Keaton-Ruthardt/Masters_Thesis/references/smart_baseball_references.md

# Smart Baseball / Instrumented Ball References

Compiled for MastersBall thesis project. Organized by topic.

---

## McGinnis IMU Baseball (University of Michigan)

- McGinnis, R.S.; Perkins, N.C. "A Highly Miniaturized, Wireless Inertial Measurement Unit for Characterizing the Dynamics of Pitched Baseballs and Softballs." *Sensors* 2012, 12(9), 11933–11945. https://www.mdpi.com/1424-8220/12/9/11933
- PMC Full Text: https://pmc.ncbi.nlm.nih.gov/articles/PMC3478818/
- McGinnis, R.S.; Perkins, N.C. "Pitcher Training Aided by Instrumented Baseball." *Procedia Engineering* 2012, 34, 580–585. (9th ISEA Conference). https://www.sciencedirect.com/science/article/pii/S1877705812017122
- McGinnis, R.S. "Advancing Applications of IMUs in Sports Training and Biomechanics." PhD Dissertation, University of Michigan, 2013. https://deepblue.lib.umich.edu/handle/2027.42/97947
- McGinnis, R.S.; Perkins, N.C.; King, K. "Miniaturized Wireless IMU Enables Low-Cost Baseball Pitching Training Aid." 35th Annual Meeting of the American Society of Biomechanics, Long Beach, CA, 2011. https://www.researchgate.net/publication/266458149_Miniaturized_Wireless_IMU_Enables_Low-Cost_Baseball_Pitching_Training_Aid
- King, K.; Yoon, S.W.; Perkins, N.C.; Najafi, K. "Wireless MEMS Inertial Sensor System for Golf Swing Dynamics." *Sensors and Actuators A: Physical* 2008, 141(2). https://www.sciencedirect.com/science/article/abs/pii/S092442470700667X
- King, K.; Perkins, N.C.; Churchill, H.; McGinnis, R.; Doss, R. "Bowling Ball Dynamics Revealed by Miniature Wireless MEMS Inertial Measurement Unit." *Sports Engineering* 2011, 13, 95–104. https://link.springer.com/article/10.1007/s12283-010-0054-z
- King, K.; Hough, J.; McGinnis, R.; Perkins, N.C. "A New Technology for Resolving the Dynamics of a Swinging Bat." *Sports Engineering* 2012, 15, 41–52.
- Perkins Lab Website (Athletic Performance): https://kmperk.wixsite.com/perkins/athletic-performance
- Perkins Faculty Page, U-M Mechanical Engineering: https://me.engin.umich.edu/people/faculty/noel-perkins/
- McGinnis Google Scholar: https://scholar.google.com/citations?user=IA5-EMcAAAAJ&hl=en

---

## Diamond Kinetics

### Patents
- US 7,021,140 — "Electronic measurement of the motion of a moving body of sports equipment." Perkins, N.C. Assignee: Regents of the University of Michigan. 2006. https://patents.google.com/patent/US7021140B2/en
- US 7,234,351 B2 — "Electronic measurement of the motion of a moving body of sports equipment." Perkins, N.C. Assignee: Regents of the University of Michigan. 2007. https://patents.google.com/patent/US7234351B2/en
- US 8,944,939 B2 — "Inertial Measurement of Sports Motion." Clark, W.W.; Romeiko, J.R. Assignee: University of Pittsburgh. 2015. https://patents.google.com/patent/US8944939B2/en
- US 9,032,794 B2 — "Pitcher training apparatus and method using a ball with an embedded inertial measurement unit." Perkins, N.; McGinnis, R. Assignee: Regents of the University of Michigan. 2015. https://patents.google.com/patent/US9032794B2/en
- US 10,888,735 B2 — "Calibration of initial orientation and position of sports equipment and body segments for inertial sensors." Clark, W.W.; Zhang, M.; Ressler, M. Assignee: Diamond Kinetics, Inc. 2021. https://patents.google.com/patent/US10888735B2/en
- US 11,083,951 — "Ball spin rate measurement system and method." Zhang, M.; Rittenhouse, J.M.; Ressler, M.J.; Clark, W.W. Assignee: Diamond Kinetics, Inc. 2021. https://patents.justia.com/patent/11083951
- Diamond Kinetics Patent Information Page: https://www.diamondkinetics.com/patent-information/patent

### Press & Technical Coverage
- U-M Innovation Partnerships: "U-M startup Diamond Kinetics releases PitchTracker for baseball pitching data." https://innovationpartnerships.umich.edu/stories/u-m-startup-diamond-kinetics-releases-pitchtracker-for-baseball-pitching-data/
- U-M ME: "Professor Noel Perkins' micro-sensor a game changer." https://me.engin.umich.edu/news-events/news/professor-noel-perkins-micro-sensor-game-changer/
- PittWire: "MLB, USA Softball and kids alike use a Pitt inventor's smart bats and balls." https://www.pittwire.pitt.edu/pittwire/features-articles/mlb-usa-softball-pitt-startup-diamond-kinetics
- Pitt Innovation: Diamond Kinetics Startup Profile. https://www.innovation.pitt.edu/pitt-startups/diamond-kinetics/
- Pitt Innovation Blog: "Take a Swing at Improving Human Performance." https://blog.innovation.pitt.edu/take-a-swing-at-improving-human-performance
- Technical.ly: "Diamond Kinetics founder on 10 years of rapid growth." https://technical.ly/startups/diamond-kinetics-mlb-founder-growth/
- Crain's Detroit: "With UM patent, it's better batter up." https://www.crainsdetroit.com/article/20130421/NEWS/304219991/with-um-patent-its-better-batter-up
- NextPittsburgh: "A high-tech baseball that tracks performance." https://nextpittsburgh.com/latest-news/diamond-kinetics-introduces-high-tech-baseball-pro-amateur-pitchers-track-performance/
- GeekWire: "Diamond Kinetics uses embedded sensors to help MLB batters and pitchers." https://www.geekwire.com/2018/diamond-kinetics-uses-embedded-sensors-help-mlb-batters-pitchers-improve-performance/
- Patent Forecast: "Diamond Kinetics Strikes A Deal With the MLB." https://www.patentforecast.com/2022/04/07/diamond-kinetics-strikes-a-deal-with-the-mlb/
- Driveline Baseball: "PitchTracker, Rapsodo, and Pitch Tracking Technologies." https://www.drivelinebaseball.com/2018/07/diamond-kinetics-pitchtracker-rapsodo-pitch-tracking-technologies/
- Diamond Kinetics Technology Page: https://www.diamondkinetics.com/technology
- FCC Report (FCC ID 2ABWR-DKT003): https://fcc.report/FCC-ID/2ABWR-DKT003

---

## PitchLogic (F5 Sports)

### Technical Sources
- Nordic Semiconductor Case Study: "F5 Sports baseball uses built-in sensors to give players and coaches live body movement and pitch performance metrics." https://www.nordicsemi.com/Nordic-news/2019/03/F5-Sports-baseball-uses-built-in-sensors-to-give-players-and-coaches-live-body-movement
- PitchLogic — How It Works: https://pitchlogic.com/howitworks
- PitchLogic — Metrics: https://pitchlogic.com/metrics
- PitchLogic Pro: https://pitchlogic.com/pitchlogic-pro
- F5 Sports Durability Test (One Year): https://pitchlogic.com/blogs/a-durability-test-on-the-pitchlogic-baseball-one-year-later

### Validation & Reviews
- Samford University Center for Sports Analytics: "Validating pitchLogic: Assessing the New Smart Baseball." 2020. https://www.samford.edu/sports-analytics/fans/2020/Validating-pitchLogic-Assessing-the-New-Smart-Baseball
- Driveline Baseball: "PitchLogic" (practical usage guide). 2022. https://www.drivelinebaseball.com/2022/07/pitchlogic/
- Baseball Aerodynamics Blog: "Training Kids with Smart Baseballs" (Post 71). 2021. https://baseballaero.com/2021/11/13/training-kids-with-smart-baseballs-post-71/
- TopVelocity: "Pitch Tracking Technologies: Trackman, Rapsodo & More." 2024. https://www.topvelocity.net/2024/05/16/pitch-tracking-technologies-trackman-rapsodo-more/
- The Robby Row Show: PitchLogic Review. https://therobbyrowshow.com/pitch-logic/

### Company & Press
- WRAL TechWire: "W-S sports tech company F5 Sports continues to fundraise, now with newly patented pitchLogic system." 2022. https://wraltechwire.com/2022/06/24/w-s-sports-tech-company-f5-sports-continues-to-fundraise-now-with-newly-patented-pitchlogic-system/
- Wake Forest Baseball Partnership: https://godeacs.com/news/2023/9/18/wake-forest-university-baseball-to-utilize-f5-sports-pitchlogic-smart-baseball
- ABCA Partnership: https://www.abca.org/ABCA/ABCA/News/2023/ABCA_and_pitchLogic_Announce_New_Partnership.aspx
- Apple App Store: https://apps.apple.com/us/app/pitchlogic/id1448402158

---

## 2024 MDPI Force Sensor Baseball

- "Sensor-Embedded Baseball for Measurement of Finger Force Characteristics." *Sensors* 2024, 24(11), 3523. https://www.mdpi.com/1424-8220/24/11/3523
- PMC: https://pmc.ncbi.nlm.nih.gov/articles/PMC11175286/

---

## Smart Cricket Balls

- Fuss, F.K.; Lythgo, N.; Smith, R.M.; Benson, A.C.; Gordon, B. "Development of a Smart Cricket Ball for Advanced Performance Analysis of Bowling." *Procedia Technology* 2015, 20, 133–137. https://www.researchgate.net/publication/283271775_Development_of_a_Smart_Cricket_Ball_for_Advanced_Performance_Analysis_of_Bowling
- Fuss, F.K. et al. "Mobile Computing with a Smart Cricket Ball: Discovery of Novel Performance Parameters and Their Practical Application to Performance Analysis, Advanced Profiling, Tactical Insights, and Talent Identification of Spin Bowlers." *Sensors* 2021, 21(20), 6942. https://www.mdpi.com/1424-8220/21/20/6942
- Nordic Semiconductor: "Sportcor SmartBall employs nRF52840 to send tracking data from Kookaburra Sports SmartBall to app." https://www.nordicsemi.com/Nordic-news/2019/10/Sportcor-Smartball-employs-nRF52840-to-send-tracking-data-from-Kookaburra-Sports-Smartball-to-app
- Electronics Weekly: "Smart Cricket Ball Measures Bowling Performance." https://www.electronicsweekly.com/blogs/gadget-master/sensors/smart-cricket-ball-measures-bowling-performance-2020-01/

---

## Smart Golf Balls & Other Smart Sports Balls

- GENIUS Golf Ball (OnCore): https://geniusball.golf/
- OnCore Golf Technology / Patents: https://www.oncoregolf.com/technology/
- First Call Golf: "The First Smart Golf Ball That Captures Crucial Putting Data — GENIUS." 2026. https://www.firstcallgolf.com/industry-news/release/2026-01-15/the-first-smart-golf-ball-that-captures-crucial-putting-data-genius-to-make-groundbreaking-debut-at-pg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
- Smart Golf Ball with Embedded Microsystem (University Project, MCEN 4228): http://mirandabutler.github.io/img/mechanical/MSreport.pdf
- Fraunhofer: Microsystem Technologies for Smart Golf Balls ("eGrains"). https://publica.fraunhofer.de/entities/publication/e8bcb660-518a-4688-a181-c66124ebc0aa
- SoccerBible: "Closer Look — Adidas miCoach Smart Ball." https://www.soccerbible.com/performance/football-equipment/closer-look-adidas-micoach-smartball/

---

## Baseball Physics & Biomechanics

- Penn State — Forces Between Bat and Ball (Dr. Dan Russell): https://www.acs.psu.edu/drussell/bats/impulse.html
- University of Illinois — Dynamics of the Baseball-Bat Collision (Prof. Alan Nathan): https://baseball.physics.illinois.edu/AJP-Nov2000.pdf
- University of Illinois — Baseball Aerodynamics: https://baseball.physics.illinois.edu/aero.html
- NASA — Forces on a Baseball (Beginner's Guide to Aeronautics): https://www1.grc.nasa.gov/beginners-guide-to-aeronautics/forces-on-a-baseball/
- ACS — "What's in Baseballs: Materials Explain the Spike in Home Runs." *Chemical & Engineering News* 2017, 95(26). https://cen.acs.org/articles/95/i26/s-baseballs-materials-explain-spike.html
- Baseball Rules Academy — Official Rule 3.01 (The Ball): https://baseballrulesacademy.com/official-rule/mlb/3-01-the-ball/
- University of Illinois — Inertial Sensors in Baseball: https://baseball.physics.illinois.edu/batsensors.html
- MIT Media Lab — "IMU Arrays: The Biomechanics of Baseball Pitching." Paradiso, J. et al. 2006. https://www.media.mit.edu/publications/imu-arrays-the-biomechanics-of-baseball-pitching/
- MIT Media Lab PDF: https://resenv.media.mit.edu/pubs/papers/2006-06-IMU-Baseball.pdf

---

## High-g Sensor Technology & Shock Survival

- Analog Devices — "Surviving the Extremes" (MEMS in High-Shock Environments): https://www.analog.com/en/resources/analog-dialogue/articles/surviving-the-extremes.html
- ADXL375 High-g Accelerometer (200g, digital): https://www.adafruit.com/product/5374
- Blast Motion Bat Sensor (10,000g survival housing): https://blastmotion.com/products/baseball/
- Garmin Impact Bat Sensor: https://www.garmin.com/en-US/p/579018/

---

## Sensor Datasheets (Components in MastersBall Project)

- King et al. — Instrumented Cricket Ball Spin Measurement (19×24mm PCB, 3g): https://www.sciencedirect.com/science/article/pii/S1877705812016360

---

*Last updated: March 2026*
*Compiled for MastersBall instrumented baseball thesis project*
