Keaton-Ruthardt/Masters_Thesis/hardware/smartball_PCB.pdf

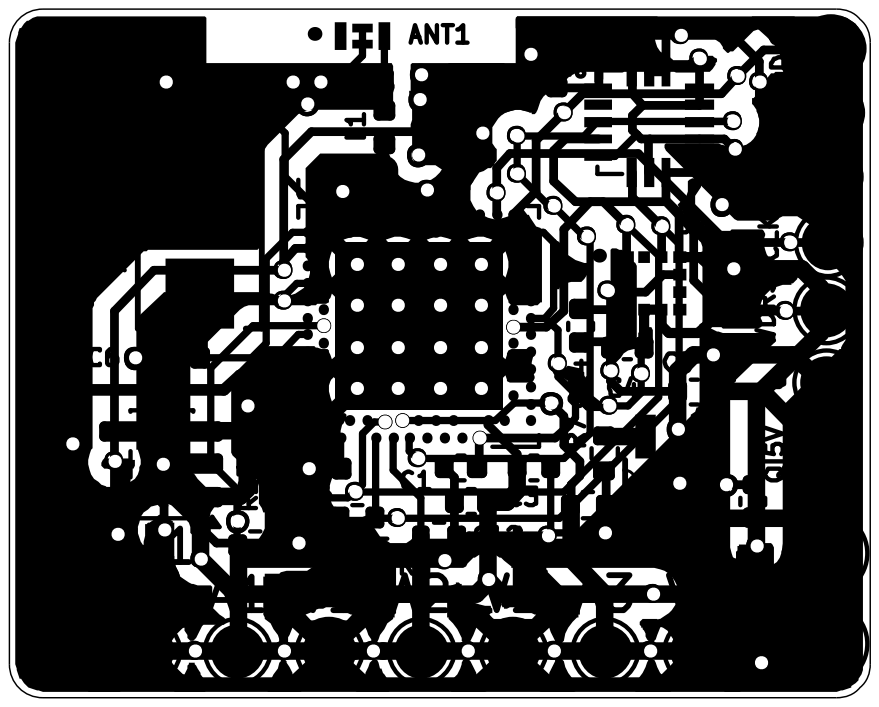
[picture p14: page 1]
