Keaton-Ruthardt/Masters_Thesis/figures/wiring+xaio+usb-c-adapater.jpeg

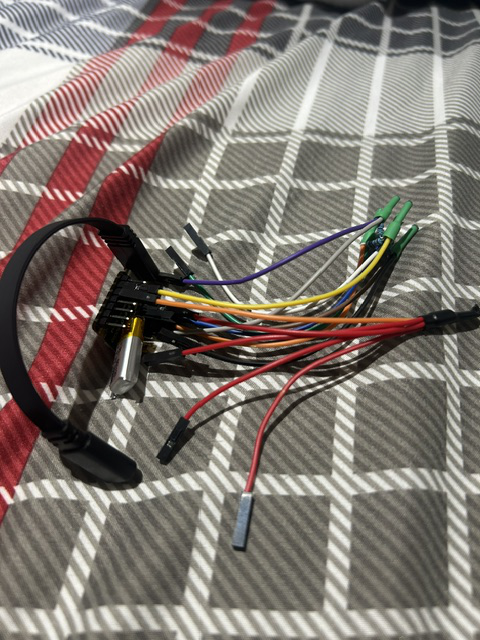
figures/wiring+xaio+usb-c-adapater.jpeg
