Keaton-Ruthardt/Masters_Thesis/analysis/results/per_pitch_features.csv

pitcher | pitch_type | t_start | t_end | n_samples | pointer_peak_N | pointer_F_rel_N | pointer_t_rel | pointer_impulse_Ns | pointer_RFD_Ns | middle_peak_N | middle_F_rel_N | middle_t_rel | middle_impulse_Ns | middle_RFD_Ns | thumb_peak_N | thumb_F_rel_N | thumb_t_rel | thumb_impulse_Ns | thumb_RFD_Ns | thumb_lead_ms | pointer_middle_gap_ms | total_peak_N | CV_peak | pointer_share | middle_share | thumb_share | finger_peak_N | finger_F_rel_N | finger_impulse_Ns | finger_RFD_Ns | thumb_finger_ratio | velo_mph | spin_rpm | hz_break | ivb | effort_pct | raw_tag | effort_source | warmup | paired | analyzable
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
