Keaton-Ruthardt/Masters_Thesis/analysis/results/release_force_variants.csv

pitcher | pitch_type | t_end | pointer_peak | pointer_F5 | pointer_J5 | pointer_F10 | pointer_J10 | pointer_F25 | pointer_J25 | pointer_F50 | pointer_J50 | pointer_F100 | pointer_J100 | pointer_secpk | pointer_unload | middle_peak | middle_F5 | middle_J5 | middle_F10 | middle_J10 | middle_F25 | middle_J25 | middle_F50 | middle_J50 | middle_F100 | middle_J100 | middle_secpk | middle_unload | thumb_peak | thumb_F5 | thumb_J5 | thumb_F10 | thumb_J10 | thumb_F25 | thumb_J25 | thumb_F50 | thumb_J50 | thumb_F100 | thumb_J100 | thumb_secpk | thumb_unload | finger_peak | finger_F5 | finger_J5 | finger_F10 | finger_J10 | finger_F25 | finger_J25 | finger_F50 | finger_J50 | finger_F100 | finger_J100 | finger_secpk | finger_unload | velo_mph | effort_pct | analyzable
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
